njhulsey/Ardu-Controller/GameController/include/Game.h

#include <Adafruit_GFX.h>
#include <Adafruit_SSD1305.h>
//#include "Main.h"

//Adafruit_SSD1305 display;
void gameStart();
void tick();
void render();


/*
static const unsigned char PROGMEM animal[] = {
B00000010, B11000000,
B00000001, B10110000,
B00000011, B11110000,
B00000011, B11110000,
B00000011, B10000000,
B00000011, B00000000,
B00000011, B00000000,
B00000011, B00000000,
B00000011, B00000000,
B00111111, B10000000,
B01111111, B10000000,
B01111111, B10000000,
B11111111, B10000000,
B11100111, B00000000,
B11000011, B00000000,
B11000011, B00000000 };

*/
